silicium-org/occitel_mini/historical/drawings/Occitel_Mini_-_DEFINITIVE_2023-Mar-13_05-27-04PM-000_CustomizedView18084922699.png

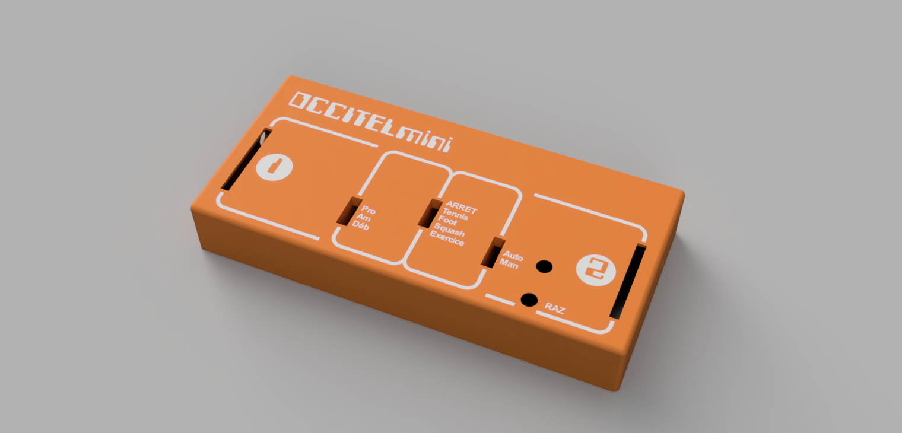
historical/drawings/Occitel_Mini_-_DEFINITIVE_2023-Mar-13_05-27-04PM-000_CustomizedView18084922699.png
